alxhou/myPlant/Firmware/ConfigStore.h

/**************************************************************
 * This is a DEMO. You can use it only for development and testing.
 *
 * If you would like to add these features to your product,
 * please contact Blynk for Business:
 *
 *                  http://www.blynk.io/
 *
 **************************************************************/

struct ConfigStore {
  uint32_t  magic;
  char      version[9];
  uint8_t   flagConfig:1;
  uint8_t   flagApFail:1;
  uint8_t   flagSelfTest:1;

  char      wifiSSID[34];
  char      wifiPass[34];

  char      cloudToken[34];
  char      cloudHost[34];
  uint16_t  cloudPort;

  char      plantName[34];
  char      plantCoordinate[34];

  uint16_t  state;
  uint16_t  counter;

  uint16_t  checksum;
} __attribute__((packed));

ConfigStore configStore;

const ConfigStore configDefault = {
  0x626C6E6B,
  BOARD_FIRMWARE_VERSION,
  0, 0, 0,
  
  "",
  "",
  
  "invalid token",
  "blynk-cloud.com", 8442,
  "plant",
  "0,0",
  1,
  0,
  0 
};

#include <EEPROM.h>
#define EEPROM_CONFIG_START 0

void config_load()
{
  EEPROM.get(EEPROM_CONFIG_START, configStore);
  if (configStore.magic != configDefault.magic) {
    DEBUG_PRINT("Using default config.");
    configStore = configDefault;
    return;
  }
}

bool config_save()
{
  EEPROM.put(EEPROM_CONFIG_START, configStore);
  EEPROM.commit();
  return true;
}

bool config_init()
{
  EEPROM.begin(sizeof(ConfigStore));
  config_load();
  return true;
}

void config_reset()
{
  DEBUG_PRINT("Resetting configuration!");
  configStore = configDefault;
  config_save();
  BlynkState::set(MODE_WAIT_CONFIG);
}

template<typename T, int size>
void CopyString(const String& s, T(&arr)[size]) {
  s.toCharArray(arr, size);
}
